BRISINGR-01/joystick-mouse/hardware/design/output/3D-bottom.png

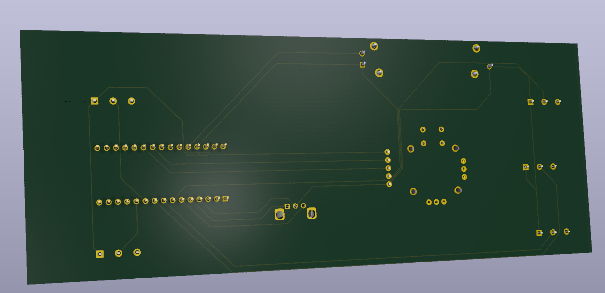
hardware/design/output/3D-bottom.png
