BRISINGR-01/joystick-mouse/hardware/design/output/3D-top.png

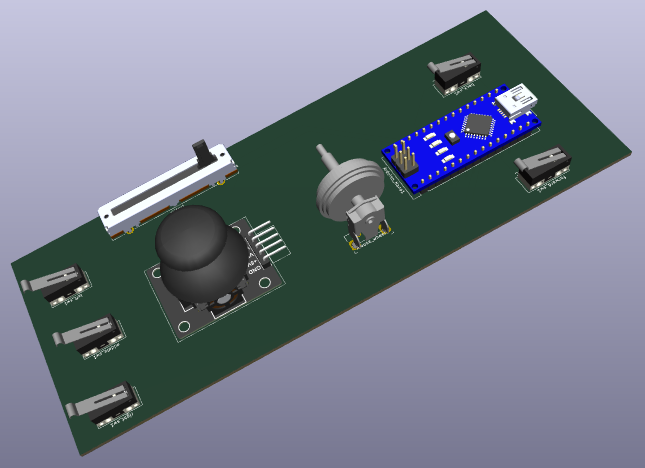
hardware/design/output/3D-top.png
